rorromr/ei4001/test/TorsoController/TorsoController.ino

#define LOGGER_MIN_SEVERITY LOGGER_SEVERITY_INFO
#include <SerialDXL.h>
#include <SimpleEncoder.h>
#include <HBridge.h>
#include <Fin_de_Carrera.h>
#include <DPID.h>
#include "DigitalIO.h"

# define MOTOR_PWM_R 9
# define MOTOR_PWM_L 10
# define ENCODER_A 2
# define ENCODER_B 4
# define FDC1 28
# define FDC2 30
# define FDC3 32
# define FDC4 34

# define FDC2_pos 5000 
# define FDC3_pos 0

// Torso basic config
#define TORSO_MODEL 100
#define TORSO_FIRMWARE 100
#define TORSO_MMAP_SIZE 10

DigitalPin<13> pin13;

enum statemachine {
  INIT,
  CHECK,
  ERROR,
  MOVE,
  STATE
};

enum statemachine sm;

typedef DeviceDXL<TORSO_MODEL, TORSO_FIRMWARE, TORSO_MMAP_SIZE> TorsoType;


/**
 * @brief Torso controller using DXL communication protocol
 * @details Torso controller using Dynamixel communication protocol over RS485.
 * This implementation uses a 1 uint8_t variable for Torso reference in address 6
 * of memory map (MMap).
 *
 * @param dir_pin Toggle communication pin.
 * @param reset_pin Pin for reset device
 */
class TorsoDXL: public TorsoType
{
  public:
    TorsoDXL(uint8_t dir_pin, uint8_t reset_pin, Encoder *encoder, DFILTERS::DPID *pid, HBridge *hbridge, Fin_de_Carrera *fdc):
      DeviceDXL(), // Call parent constructor
      dir_pin_(dir_pin),    // Direction pin for RS485
      reset_pin_(reset_pin), // Reset pin
      encoder_(encoder), //Puntero a objetos
      pid_(pid),
      hbridge_(hbridge),
      fdc_(fdc),
      goalPosition_(MMap::Access::RW, MMap::Storage::RAM),  // Torso command
      movingSpeed_(MMap::Access::RW, MMap::Storage::RAM),
      presentPosition_(MMap::Access::R, MMap::Storage::RAM),
      presentSpeed_(MMap::Access::R, MMap::Storage::RAM),
      lastPosition_(MMap::Access::R, MMap::Storage::RAM),
      kp_(MMap::Access::RW, MMap::Storage::RAM),
      ki_(MMap::Access::RW, MMap::Storage::RAM),
      kv_(MMap::Access::RW, MMap::Storage::RAM),
      limits_(MMap::Access::RW, MMap::Storage::RAM),
      emergencyState_(MMap::Access::R, MMap::Storage::RAM)
    {
      // PID Config
      pid_->setDeadZone(30);
      pid_->enableDeadZone(true);
      
    }

    void init()
    {
      // Config pins
      pinMode(dir_pin_, OUTPUT);
      pinMode(reset_pin_, OUTPUT);
      // Config PWM to 4 Khz
      hbridge_->setPwmFrequency(2);
      
      DEBUG_PRINTLN("INIT");
      /*
       * Register variables
       */
      DeviceDXL::init();
      mmap_.registerVariable(&goalPosition_);
      mmap_.registerVariable(&movingSpeed_);
      mmap_.registerVariable(&presentPosition_);
      mmap_.registerVariable(&presentSpeed_);
      mmap_.registerVariable(&emergencyState_);
      mmap_.registerVariable(&lastPosition_);
      mmap_.registerVariable(&limits_);
      mmap_.registerVariable(&kp_);
      mmap_.registerVariable(&ki_);
      mmap_.registerVariable(&kv_);
      mmap_.init();
      /*
       * Control table
       * 
       * Variable         | Offset | Size |  Type |
       * ------------------------------------------
       * goalPosition_    | 6      | 4    | int32 |
       * movingSpeed_     | 10     | 1    | int8  |
       * presentPosition_ | 11     | 4    | int32 |
       * presentSpeed_    | 15     | 1    | int8  |
       * emergencyState_  | 16     | 1    | uint8 |
       * lastPosition_    | 17     | 4    | int32 |
       * limits_          | 21     | 1    | uint8 |
       * kp_              | 22     | 4    | float |
       * ki_              | 26     | 4    | float |
       * kv_              | 30     | 4    | float |
       * 
       */

      /*
       * Load default values
       */
      DEBUG_PRINTLN("Load default");
      mmap_.load(); // Load values from EEPROM
      presentPosition_.data = lastPosition_.data;
      //DEBUG_PRINT("data: ");DEBUG_PRINTLN(command_.data);

      /*
       * Read sensor data
       * e.g. Use ADC, check buttons, etc.
       */
      // Set PID Limits
      pid_->setLimit(limits_.data);
      
    }

    void update()
    {
      static uint32_t last_call = 0UL;
      if (micros()-last_call<1000)
        return;
      last_call = micros();

      pin13.high();
      mmap_.deserialize();
      presentPosition_.data = encoder_->read();
      pid_->update(goalPosition_.data - presentPosition_.data);
      hbridge_->set( (int16_t) pid_->getOutputAntiwindup());
      mmap_.serialize();
      pin13.low();
      /*
      switch (sm) {
        case INIT:
          sm = CHECK;
          break;

        case CHECK:
          presentPosition_.data = encoder_->read();
          
          if (fdc_->getState()) {
            emergencyState_.data = 1;
            sm = ERROR;
          }
          else {
            emergencyState_.data = 0;
            sm = MOVE;
          }
          break;

        case ERROR:
          switch (fdc_->getIndex()) {
            case 1:
              hbridge_->activeBrake();
              // Pasar a modo manual
              pid_->restart();

              break;

            case 2:
              hbridge_->activeBrake(); //Cuanto seguirá subiendo por inercia?
              pid_->restart();
              encoder_->write(FDC2_pos);
              presentPosition_.data = FDC2_pos;
              goalPosition_.data = presentPosition_.data - 5000;  // Solo de prueba, que baje 5 cm en realidad
              sm = MOVE;
              break;

            case 3:
              hbridge_->activeBrake();
              pid_->restart();
              encoder_->write(FDC3_pos);
              presentPosition_.data = FDC3_pos;
              goalPosition_.data = presentPosition_.data + 720;  // Solo de prueba, que suba 5 cm en realidad
              sm = MOVE;

              break;

            case 4:
              hbridge_->activeBrake();
              // Pasar a modo manual
              pid_->restart();

              break;
          }
          break;

        case MOVE:

          pid_->update(goalPosition_.data - presentPosition_.data);
          hbridge_->set( (int16_t) pid_->getOutputAntiwindup());
          //presentSpeed_.data = (int8_t) pid_->getOutputAntiwindup();
          emergencyState_.data = pid_->isDeadZone() ? 0 : 1;
          sm = emergencyState_.data == 1? MOVE : STATE; 
          break;

        case STATE:
          sm = CHECK;
          break;

      }
      */

    }

    inline bool onReset()
    {
      return digitalRead(reset_pin_) == HIGH ? true : false;
    }

    inline void setTX()
    {
      digitalWrite(dir_pin_, HIGH);
    }

    inline void setRX()
    {
      digitalWrite(dir_pin_, LOW);
    }

  private:
    const uint8_t dir_pin_; // Toggle communication direction pin
    const uint8_t reset_pin_; // Reset pin

    Encoder *encoder_;
    DFILTERS::DPID *pid_;
    HBridge *hbridge_;
    Fin_de_Carrera *fdc_;

    // Torso command
    MMap::Integer<Int32,-100000,100000, 0>::type goalPosition_;
    MMap::Integer<Int8,  -127,  127,    0>::type movingSpeed_;
    MMap::Integer<Int32,-100000,100000, 0>::type presentPosition_;
    MMap::Integer<Int8,  -127,  127,   -20>::type presentSpeed_;
    MMap::Integer<UInt8, 0,     1,      0>::type emergencyState_;
    MMap::Integer<Int32, 0,     57600,  0>::type lastPosition_;
    MMap::Integer<UInt8, 0,     255,    0>::type limits_;
    MMap::Float<ConstRatio<0,1>, ConstRatio<1000,1>, ConstRatio<9,10>   >::type kp_;
    MMap::Float<ConstRatio<0,1>, ConstRatio<1000,1>, ConstRatio<15,100> >::type ki_;
    MMap::Float<ConstRatio<0,1>, ConstRatio<1000,1>, ConstRatio<15,100> >::type kv_;
};

// PID constants
float kp = 1.0;
float kv = 0.01;//0.08;
float ki = 0.00;//0.1;
float Ts = 0.001;
int discretization_method = 4;
float limit = 255;
float kaw = sqrt(ki*kv);
  

// Controller
DFILTERS::DPID pid(kp, kv, ki, Ts, discretization_method, limit, kaw);

// Encoder
Encoder encoder(ENCODER_A, ENCODER_B);

// H bridge class
HBridge hbridge(MOTOR_PWM_R, MOTOR_PWM_L);

// Clase Fin de carrera
Fin_de_Carrera fdc(FDC1, FDC2, FDC3, FDC4);

// Torso Controller
TorsoDXL torso(7, 6, &encoder, &pid, &hbridge, &fdc);

SerialDXL<TorsoDXL> serialDxl;

void setup() {
  Serial.begin(115200);
  pin13.mode(OUTPUT);

  torso.init();
  torso.reset();
  torso.mmap_.serialize();
  
  // Init serial communication using Dynamixel format
  serialDxl.init(&Serial3 , &torso);
}

void loop() {
  // Update msg buffer
  
  while (Serial3.available())
    serialDxl.process(Serial3.read());

  
  torso.update();
}
